Mark-MDO47/Know-How-Arduino-SteamPunk-Goggles/KiCad/SteamPunkGoggles/SteamPunkGoggles.kicad_pcb

## KiCad design multianem8/cta.kicad_pcb



Parts:
CI1, CI2, CI3, CI4, CI9, CI10, CI11, CI12: 100n; C_Rect_L7.2mm_W3.5mm_P5.00mm_FKS2_FKP2_MKS2_MKP2
Cf1, Cf2, Cf3, Cf4, Cf9, Cf10, Cf11, Cf12: 1u; CP_Radial_D5.0mm_P2.50mm
Coo1: 10u; CP_Radial_D5.0mm_P2.50mm
Cua1, Cua2, Cua3, Cua4, Cua9, Cua10, Cua11, Cua12: 100n; C_Disc_D5.0mm_W2.5mm_P2.50mm
Cub1, Cub2, Cub3, Cub4, Cub9, Cub10, Cub11, Cub12: 100n; C_Disc_D5.0mm_W2.5mm_P2.50mm
D1: 1N4001; D_DO-41_SOD81_P10.16mm_Horizontal
Don1, Don2, Don3, Don4, Don9, Don10, Don11, Don12: 1N4148; D_DO-35_SOD27_P7.62mm_Horizontal
JOUT1: Conn_01x09; PinHeader_1x09_P2.54mm_Vertical
JVIN1: Conn_01x06; TerminalBlock_bornier-6_P5.08mm
Jw1, Jw2, Jw3, Jw4, Jw9, Jw10, Jw11, Jw12: Conn_01x02; PinHeader_1x02_P2.54mm_Vertical
Q1, Q2, Q3, Q4, Q9, Q10, Q11, Q12: TIP41; TO-220-3_Vertical
Qon1: 2N3906; TO-92_Inline_Wide
Ra1, Ra2, Ra3, Ra4, Ra9, Ra10, Ra11, Ra12: 100; R_Axial_DIN0207_L6.3mm_D2.5mm_P10.16mm_Horizontal
Rb1, Rb2, Rb3, Rb4, Rb9, Rb10, Rb11, Rb12: 10; R_Axial_DIN0414_L11.9mm_D4.5mm_P15.24mm_Horizontal
Rc1, Rc2, Rc3, Rc4, Rc9, Rc10, Rc11, Rc12: 1k; R_Axial_DIN0207_L6.3mm_D2.5mm_P10.16mm_Horizontal
Rda1, Rda2, Rda3, Rda4, Rda9, Rda10, Rda11, Rda12: 100k; R_Axial_DIN0207_L6.3mm_D2.5mm_P10.16mm_Horizontal
Rdb1, Rdb2, Rdb3, Rdb4, Rdb9, Rdb10, Rdb11, Rdb12: 20k; R_Axial_DIN0207_L6.3mm_D2.5mm_P10.16mm_Horizontal
Rf1, Rf2, Rf3, Rf4, Rf9, Rf10, Rf11, Rf12: 10k; R_Axial_DIN0207_L6.3mm_D2.5mm_P10.16mm_Horizontal
Roo1: 100; R_Axial_DIN0207_L6.3mm_D2.5mm_P10.16mm_Horizontal
Roo2: 22k; R_Axial_DIN0207_L6.3mm_D2.5mm_P10.16mm_Horizontal
Roo3: 4.7k; R_Axial_DIN0207_L6.3mm_D2.5mm_P10.16mm_Horizontal
Rt1, Rt2, Rt3, Rt4, Rt9, Rt10, Rt11, Rt12: 2k; R_Axial_DIN0207_L6.3mm_D2.5mm_P10.16mm_Horizontal
Rua1, Rua2, Rua3, Rua4, Rua9, Rua10, Rua11, Rua12: 10k; R_Axial_DIN0207_L6.3mm_D2.5mm_P10.16mm_Horizontal
Rub1, Rub2, Rub3, Rub4, Rub9, Rub10, Rub11, Rub12: 10k; R_Axial_DIN0207_L6.3mm_D2.5mm_P10.16mm_Horizontal
U1, U2, U3, U4, U9, U10, U11, U12: LM324; DIP-14_W7.62mm_LongPads

Connections:
/VO1: JOUT1.1, U1.6 (-), U1.7
/VO2: JOUT1.2, U2.6 (-), U2.7
/VO3: JOUT1.3, U3.6 (-), U3.7
/VO4: JOUT1.4, U4.6 (-), U4.7
/VO9: JOUT1.8, U9.6 (-), U9.7
/VO10: JOUT1.7, U10.6 (-), U10.7
/VO11: JOUT1.6, U11.6 (-), U11.7
/VO12: JOUT1.5, U12.6 (-), U12.7
/VON1: Don1.2 (A), Don2.2 (A), Don3.2 (A), Don4.2 (A), Don9.2 (A), Don10.2 (A), Don11.2 (A), Don12.2 (A), Qon1.3 (C)
GND: Cf1.2, Cf2.2, Cf3.2, Cf4.2, Cf9.2, Cf10.2, Cf11.2, Cf12.2, Coo1.2, Cua1.2, Cua2.2, Cua3.2, Cua4.2, Cua9.2, Cua10.2, Cua11.2, Cua12.2, Cub1.2, Cub2.2, Cub3.2, Cub4.2, Cub9.2, Cub10.2, Cub11.2, Cub12.2, JOUT1.9, JVIN1.5, JVIN1.6, Jw1.2, Jw2.2, Jw3.2, Jw4.2, Jw9.2, Jw10.2, Jw11.2, Jw12.2, Rc1.2, Rc2.2, Rc3.2, Rc4.2, Rc9.2, Rc10.2, Rc11.2, Rc12.2, Rdb1.2, Rdb2.2, Rdb3.2, Rdb4.2, Rdb9.2, Rdb10.2, Rdb11.2, Rdb12.2, Roo3.2
unnamed: CI1.1, Rt1.1, U1.1
unnamed: CI1.2, Rua1.1, U1.2 (-)
unnamed: CI2.1, Rt2.1, U2.1
unnamed: CI2.2, Rua2.1, U2.2 (-)
unnamed: CI3.1, Rt3.1, U3.1
unnamed: CI3.2, Rua3.1, U3.2 (-)
unnamed: CI4.1, Rt4.1, U4.1
unnamed: CI4.2, Rua4.1, U4.2 (-)
unnamed: CI9.1, Rt9.1, U9.1
unnamed: CI9.2, Rua9.1, U9.2 (-)
unnamed: CI10.1, Rt10.1, U10.1
unnamed: CI10.2, Rua10.1, U10.2 (-)
unnamed: CI11.1, Rt11.1, U11.1
unnamed: CI11.2, Rua11.1, U11.2 (-)
unnamed: CI12.1, Rt12.1, U12.1
unnamed: CI12.2, Rua12.1, U12.2 (-)
unnamed: Cf1.1, Rf1.1, U1.5 (+)
unnamed: Cf2.1, Rf2.1, U2.5 (+)
unnamed: Cf3.1, Rf3.1, U3.5 (+)
unnamed: Cf4.1, Rf4.1, U4.5 (+)
unnamed: Cf9.1, Rf9.1, U9.5 (+)
unnamed: Cf10.1, Rf10.1, U10.5 (+)
unnamed: Cf11.1, Rf11.1, U11.5 (+)
unnamed: Cf12.1, Rf12.1, U12.5 (+)
unnamed: Coo1.1, Roo1.1, Roo2.2
unnamed: D1.1 (K), Qon1.1 (E)
unnamed: Don1.1 (K), Q1.1 (B), Rt1.2
unnamed: Don2.1 (K), Q2.1 (B), Rt2.2
unnamed: Don3.1 (K), Q3.1 (B), Rt3.2
unnamed: Don4.1 (K), Q4.1 (B), Rt4.2
unnamed: Don9.1 (K), Q9.1 (B), Rt9.2
unnamed: Don10.1 (K), Q10.1 (B), Rt10.2
unnamed: Don11.1 (K), Q11.1 (B), Rt11.2
unnamed: Don12.1 (K), Q12.1 (B), Rt12.2
unnamed: Jw1.1, Rb1.2, Rub1.2, U1.12 (+)
unnamed: Jw2.1, Rb2.2, Rub2.2, U2.12 (+)
unnamed: Jw3.1, Rb3.2, Rub3.2, U3.12 (+)
unnamed: Jw4.1, Rb4.2, Rub4.2, U4.12 (+)
unnamed: Jw9.1, Rb9.2, Rub9.2, U9.12 (+)
unnamed: Jw10.1, Rb10.2, Rub10.2, U10.12 (+)
unnamed: Jw11.1, Rb11.2, Rub11.2, U11.12 (+)
unnamed: Jw12.1, Rb12.2, Rub12.2, U12.12 (+)
unnamed: Q1.3 (E), Ra1.1, Rb1.1
unnamed: Q2.3 (E), Ra2.1, Rb2.1
unnamed: Q3.3 (E), Ra3.1, Rb3.1
unnamed: Q4.3 (E), Ra4.1, Rb4.1
unnamed: Q9.3 (E), Ra9.1, Rb9.1
unnamed: Q10.3 (E), Ra10.1, Rb10.1
unnamed: Q11.3 (E), Ra11.1, Rb11.1
unnamed: Q12.3 (E), Ra12.1, Rb12.1
unnamed: Qon1.2 (B), Roo1.2
unnamed: Ra1.2, Rc1.1, Rua1.2
unnamed: Ra2.2, Rc2.1, Rua2.2
unnamed: Ra3.2, Rc3.1, Rua3.2
unnamed: Ra4.2, Rc4.1, Rua4.2
unnamed: Ra9.2, Rc9.1, Rua9.2
unnamed: Ra10.2, Rc10.1, Rua10.2
unnamed: Ra11.2, Rc11.1, Rua11.2
unnamed: Ra12.2, Rc12.1, Rua12.2
unnamed: Rda1.1, U1.13 (-), U1.14
unnamed: Rda1.2, Rdb1.1, U1.10 (+)
unnamed: Rda2.1, U2.13 (-), U2.14
unnamed: Rda2.2, Rdb2.1, U2.10 (+)
unnamed: Rda3.1, U3.13 (-), U3.14
unnamed: Rda3.2, Rdb3.1, U3.10 (+)
unnamed: Rda4.1, U4.13 (-), U4.14
unnamed: Rda4.2, Rdb4.1, U4.10 (+)
unnamed: Rda9.1, U9.13 (-), U9.14
unnamed: Rda9.2, Rdb9.1, U9.10 (+)
unnamed: Rda10.1, U10.13 (-), U10.14
unnamed: Rda10.2, Rdb10.1, U10.10 (+)
unnamed: Rda11.1, U11.13 (-), U11.14
unnamed: Rda11.2, Rdb11.1, U11.10 (+)
unnamed: Rda12.1, U12.13 (-), U12.14
unnamed: Rda12.2, Rdb12.1, U12.10 (+)
unnamed: Rf1.2, U1.8, U1.9 (-)
unnamed: Rf2.2, U2.8, U2.9 (-)
unnamed: Rf3.2, U3.8, U3.9 (-)
unnamed: Rf4.2, U4.8, U4.9 (-)
unnamed: Rf9.2, U9.8, U9.9 (-)
unnamed: Rf10.2, U10.8, U10.9 (-)
unnamed: Rf11.2, U11.8, U11.9 (-)
unnamed: Rf12.2, U12.8, U12.9 (-)
unnamed: Rub1.1, U1.3 (+)
unnamed: Rub2.1, U2.3 (+)
unnamed: Rub3.1, U3.3 (+)
unnamed: Rub4.1, U4.3 (+)
unnamed: Rub9.1, U9.3 (+)
unnamed: Rub10.1, U10.3 (+)
unnamed: Rub11.1, U11.3 (+)
unnamed: Rub12.1, U12.3 (+)
VCC: Cub1.1, Cub2.1, Cub3.1, Cub4.1, Cub9.1, Cub10.1, Cub11.1, Cub12.1, D1.2 (A), JVIN1.1, JVIN1.2, Q1.2 (C), Q2.2 (C), Q3.2 (C), Q4.2 (C), Q9.2 (C), Q10.2 (C), Q11.2 (C), Q12.2 (C), Roo2.1, Roo3.1, U1.4 (V+), U2.4 (V+), U3.4 (V+), U4.4 (V+), U9.4 (V+), U10.4 (V+), U11.4 (V+), U12.4 (V+)
VEE: Cua1.1, Cua2.1, Cua3.1, Cua4.1, Cua9.1, Cua10.1, Cua11.1, Cua12.1, JVIN1.3, JVIN1.4, U1.11 (V-), U2.11 (V-), U3.11 (V-), U4.11 (V-), U9.11 (V-), U10.11 (V-), U11.11 (V-), U12.11 (V-)


Board: 2 copper layers, 165.1 x 148.6 mm, 144 parts (0 on the bottom side), 103 nets.
